djh1997/proj324/docs/log/blobbounding1.png

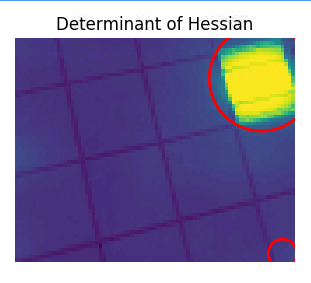
docs/log/blobbounding1.png
