djh1997/proj324/docs/log/IMG_1187.JPG

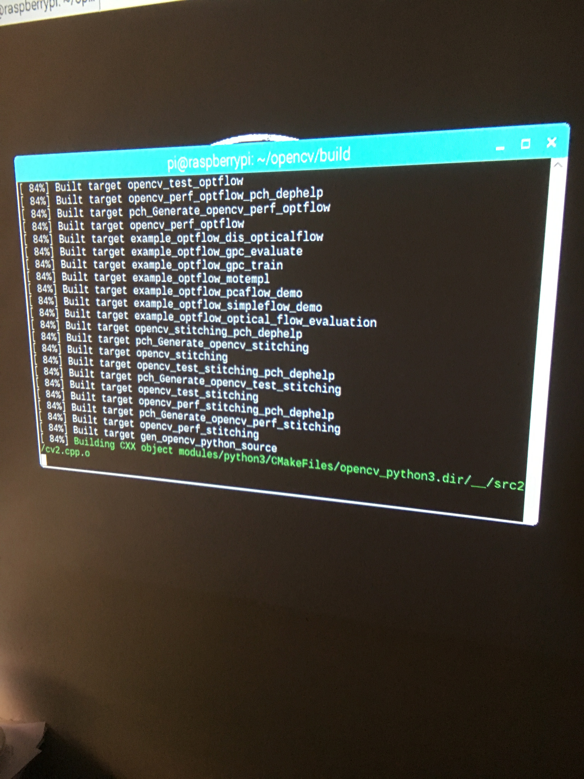
docs/log/IMG_1187.JPG
