djh1997/proj324/docs/log/IMG_1192.JPG

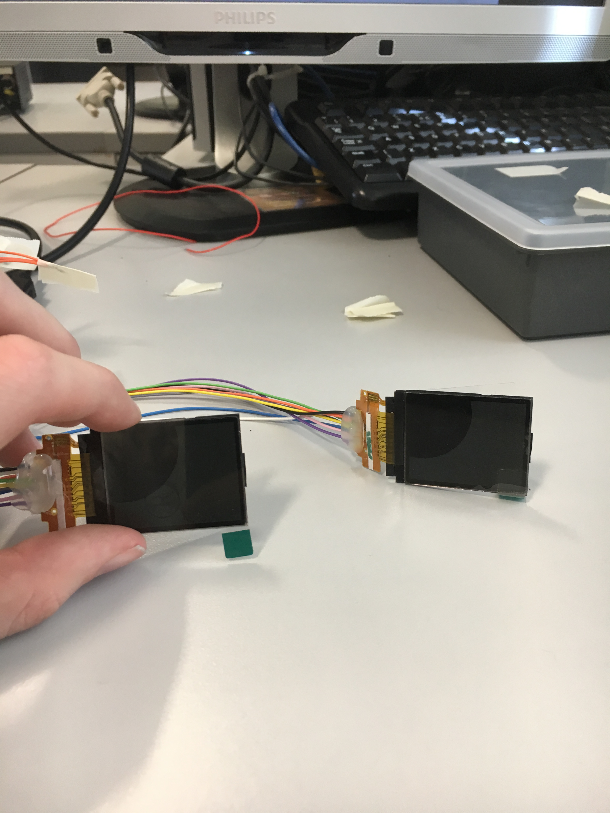
docs/log/IMG_1192.JPG
