djh1997/proj324/docs/log/IMG_1193.JPG

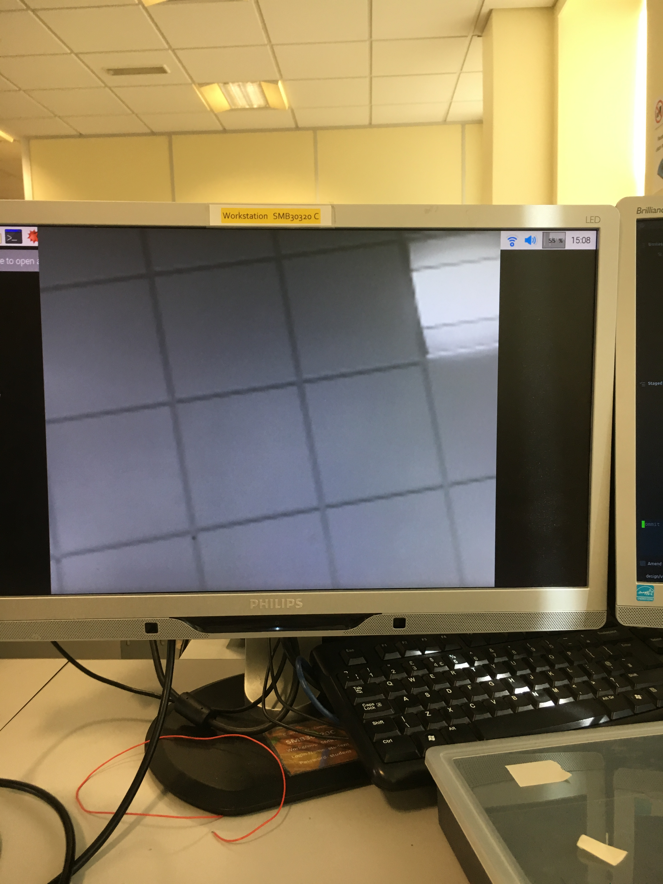
docs/log/IMG_1193.JPG
