djh1997/proj324/docs/log/IMG_1196.JPG

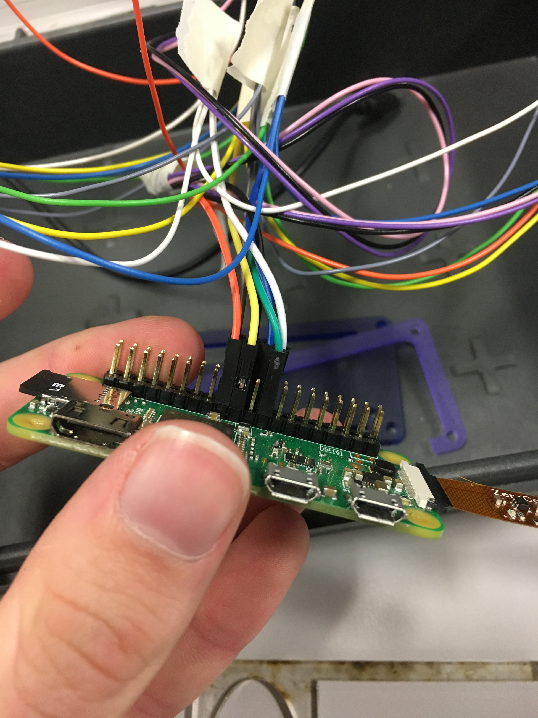
docs/log/IMG_1196.JPG
