djh1997/proj324/docs/log/IMG_1197.JPG

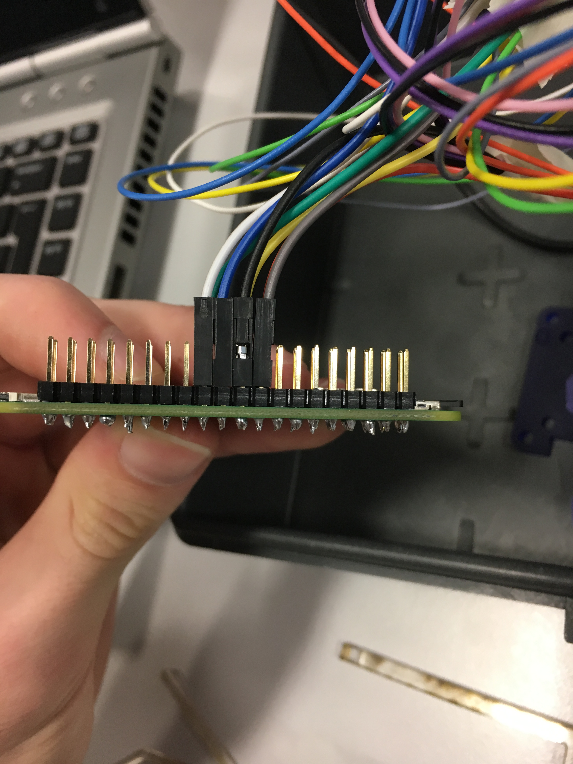
docs/log/IMG_1197.JPG
