djh1997/proj324/docs/log/IMG_1191.JPG

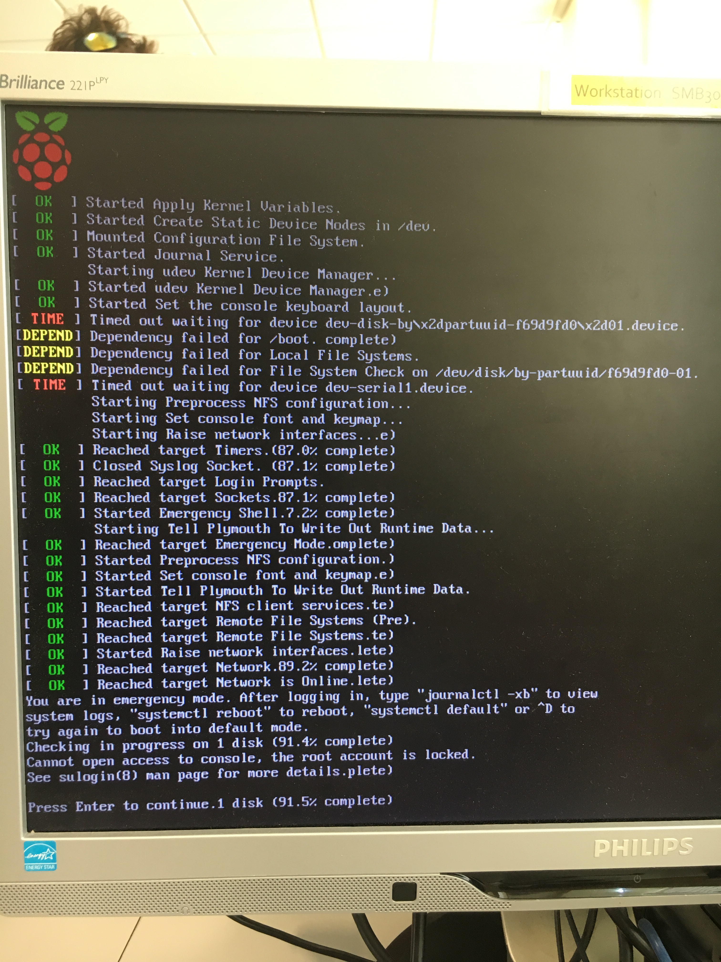
docs/log/IMG_1191.JPG
